artisdom/macro-keyboard/firmware/main/ble.c

/* This example code is in the Public Domain (or CC0 licensed, at your option.)
   Unless required by applicable law or agreed to in writing, this software is
   distributed on an "AS IS" BASIS, WITHOUT WARRANTIES OR
   CONDITIONS OF ANY KIND, either express or implied.
*/

#include <stdio.h>
#include <stdlib.h>
#include <string.h>
#include "freertos/FreeRTOS.h"
#include "freertos/task.h"
#include "freertos/event_groups.h"
#include "esp_system.h"
#include "esp_wifi.h"
#include "esp_event.h"
#include "esp_log.h"
#include "esp_bt.h"
#include "esp_bt_defs.h"
#include "esp_gap_ble_api.h"
#include "esp_gatts_api.h"
#include "esp_gatt_defs.h"
#include "esp_bt_main.h"
#include "esp_bt_device.h"
#include "driver/gpio.h"
#include "nvs_flash.h"

#include "esp_hidd_prf_api.h"
#include "hid_dev.h"

#include "ble.h"
#include "config.h"
#include "memory.h"
#include "events.h"



/* --------- Global Variables --------- */
TaskHandle_t xBLE_keyboard_task;
TaskHandle_t xBLE_media_task;
TaskHandle_t xBLE_battery_task;
TaskHandle_t xBLE_event_task;

// Input queue for sending keyboard reports
QueueHandle_t ble_keyboard_q;
// Input queue for sending media/Consumer control reports
QueueHandle_t ble_media_q;
// Input queue for sending battery reports
QueueHandle_t ble_battery_q;
// Input queue for receiving ble events to handle
QueueHandle_t ble_event_q;


/* --------- Local Defines --------- */
#define CHAR_DECLARATION_SIZE   (sizeof(uint8_t))  


/* --------- Local Variables --------- */
static const char *TAG = "ble";

static bool initialized = false;
static uint16_t hid_conn_id = 0;
static bool sec_conn = false;

static uint8_t current_host_id = 0;
static bt_host_t current_host;

static uint8_t hidd_service_uuid128[] = {
    /* LSB <--------------------------------------------------------------------------------> MSB */
    //first uuid, 16bit, [12],[13] is the value
    0xfb, 0x34, 0x9b, 0x5f, 0x80, 0x00, 0x00, 0x80, 0x00, 0x10, 0x00, 0x00, 0x12, 0x18, 0x00, 0x00,
};

static esp_ble_adv_data_t hidd_adv_data = {
    .set_scan_rsp = false,
    .include_name = true,
    .include_txpower = true,
    .min_interval = 0x0006, //slave connection min interval, Time = min_interval * 1.25 msec
    .max_interval = 0x0010, //slave connection max interval, Time = max_interval * 1.25 msec
    .appearance = 0x03c0,       //HID Generic,
    .manufacturer_len = 0,
    .p_manufacturer_data =  NULL,
    .service_data_len = 0,
    .p_service_data = NULL,
    .service_uuid_len = sizeof(hidd_service_uuid128),
    .p_service_uuid = hidd_service_uuid128,
    .flag = 0x6,
};

static esp_ble_adv_params_t hidd_adv_params = {
    .adv_int_min        = 0x20,
    .adv_int_max        = 0x30,
    .adv_type           = ADV_TYPE_IND,
    .own_addr_type      = BLE_ADDR_TYPE_PUBLIC,
    // .peer_addr          = {0x00, 0x00, 0x00, 0x00, 0x00, 0x00},
    // .peer_addr_type     = BLE_ADDR_TYPE_PUBLIC,
    .channel_map        = ADV_CHNL_ALL,
    .adv_filter_policy  = ADV_FILTER_ALLOW_SCAN_ANY_CON_ANY,
};



/* --------- Local Function --------- */
static void ble__hidd_event_callback(esp_hidd_cb_event_t event, esp_hidd_cb_param_t *param);
static void ble__gap_event_handler(esp_gap_ble_cb_event_t event, esp_ble_gap_cb_param_t *param);
static esp_err_t ble__start_advertising(esp_ble_adv_params_t *adv_params);

static void ble__set_host(uint8_t host_id);
static void ble__set_host_adv_params(bt_host_t host);

static uint8_t ble__get_last_host();
static void ble__set_last_host(uint8_t host_id);

static void ble__change_host(uint8_t host_id);
static void ble__save_host(bt_host_t host);



static void ble__hidd_event_callback(esp_hidd_cb_event_t event, esp_hidd_cb_param_t *param) {
    switch(event) {
        case ESP_HIDD_EVENT_REG_FINISH: {
            if (param->init_finish.state == ESP_HIDD_INIT_OK) {
                // esp_bd_addr_t rand_addr = {0x04,0x11,0x11,0x11,0x11,0x05};
                // esp_ble_gap_set_rand_addr(rand_addr);
                // esp_ble_gap_clear_whitelist();
                esp_ble_gap_set_device_name(BLE_DEVICE_NAME);
                esp_ble_gap_config_adv_data(&hidd_adv_data);

            }
            break;
        }
        case ESP_BAT_EVENT_REG: {
            break;
        }
        case ESP_HIDD_EVENT_DEINIT_FINISH:
            break;
        case ESP_HIDD_EVENT_BLE_CONNECT: {
            ESP_LOGI(TAG, "ESP_HIDD_EVENT_BLE_CONNECT");
            hid_conn_id = param->connect.conn_id;
            break;
        }
        case ESP_HIDD_EVENT_BLE_DISCONNECT: {
            sec_conn = false;
            ESP_LOGI(TAG, "ESP_HIDD_EVENT_BLE_DISCONNECT");
            ble__start_advertising(&hidd_adv_params);
            break;
        }
        case ESP_HIDD_EVENT_BLE_VENDOR_REPORT_WRITE_EVT: {
            ESP_LOGI(TAG, "%s, ESP_HIDD_EVENT_BLE_VENDOR_REPORT_WRITE_EVT", __func__);
            ESP_LOG_BUFFER_HEX(TAG, param->vendor_write.data, param->vendor_write.length);
        }
        default:
            break;
    }
    return;
}


static void ble__gap_event_handler(esp_gap_ble_cb_event_t event, esp_ble_gap_cb_param_t *param){
    switch (event) {
    case ESP_GAP_BLE_ADV_DATA_SET_COMPLETE_EVT:
        ble__start_advertising(&hidd_adv_params);
        break;
     case ESP_GAP_BLE_SEC_REQ_EVT:
        for(int i = 0; i < ESP_BD_ADDR_LEN; i++) {
             ESP_LOGD(TAG, "%x:",param->ble_security.ble_req.bd_addr[i]);
        }
        esp_ble_gap_security_rsp(param->ble_security.ble_req.bd_addr, true);
     break;
     case ESP_GAP_BLE_AUTH_CMPL_EVT:
        sec_conn = true;
        bt_host_t host;

        memcpy(host.addr, param->ble_security.auth_cmpl.bd_addr, sizeof(esp_bd_addr_t));
        host.type = param->ble_security.auth_cmpl.addr_type;

        ESP_LOGI(TAG, "remote host address: "ESP_BD_ADDR_STR, ESP_BD_ADDR_HEX(host.addr));
        ESP_LOGI(TAG, "address type = %d", host.type);
        ESP_LOGI(TAG, "pair status = %s",param->ble_security.auth_cmpl.success ? "success" : "fail");
        if(!param->ble_security.auth_cmpl.success) {
            ESP_LOGE(TAG, "fail reason = 0x%x",param->ble_security.auth_cmpl.fail_reason);
            sec_conn = false;
            break;
        }

        // only save if address is Public or Random
        if (host.type <= BLE_ADDR_TYPE_RANDOM) {
            ble__save_host(host);
        }
        else {
            ESP_LOGW(TAG, "Unable to save host in memory as the addr type is %d", host.type);
        }

        event_t event = {
            .type = EVENT_BT_CONNECTED,
            .data = current_host_id,
        };
        xQueueSend(event_q, (void *) &event, (TickType_t) 0);

        break;
    case ESP_GAP_BLE_REMOVE_BOND_DEV_COMPLETE_EVT:
        ESP_LOGI(TAG, "Removed bond device: %d "ESP_BD_ADDR_STR, param->remove_bond_dev_cmpl.status, ESP_BD_ADDR_HEX(param->remove_bond_dev_cmpl.bd_addr));
        break;
    default:
        // ESP_LOGD(TAG, "gap event handler: %d", *((int *)&event));
        break;
    }
}


// wrapper to call ble internal api and send an event to main event handler
static esp_err_t ble__start_advertising(esp_ble_adv_params_t *adv_params) {

    event_t event;

    if (adv_params->peer_addr[0] == 0) { // terrible check
        event.type = EVENT_BT_ADV_ALL;
    }
    else {
        event.type = EVENT_BT_ADV;
    }
    // event.type = EVENT_LEDS_BT_ADV;
    event.data = current_host_id;
    xQueueSend(event_q, (void *) &event, (TickType_t) 0);

    return esp_ble_gap_start_advertising(adv_params);
}


static uint8_t ble__get_last_host() {
    return memory__get_bluetooth_last_host();
}

static void ble__set_last_host(uint8_t host_id) {
    memory__set_bluetooth_last_host(host_id);
}


static void ble__set_host_adv_params(bt_host_t host) {

    memcpy(hidd_adv_params.peer_addr, host.addr, sizeof(host.addr));
    hidd_adv_params.peer_addr_type = host.type;
    hidd_adv_params.adv_type = ADV_TYPE_DIRECT_IND_LOW;

    ESP_LOGD(TAG, "adv peer addr: "ESP_BD_ADDR_STR, ESP_BD_ADDR_HEX(hidd_adv_params.peer_addr));
    ESP_LOGD(TAG, "adv peer addr type: %d", hidd_adv_params.peer_addr_type);

    if (host.addr[0] == 0) { //terrible check
        ESP_LOGW(TAG, "No host stored in memory, advertising to all...");
        hidd_adv_params.adv_type = ADV_TYPE_IND;
    }

}


static void ble__set_host(uint8_t host_id) {

    bt_host_t host;

    ESP_LOGI(TAG, "Setting host to %d", host_id);

    host = memory__get_bluetooth_host(host_id);
    current_host = host;
    current_host_id = host_id;

    ble__set_host_adv_params(host);

}


static void ble__change_host(uint8_t host_id) {
    esp_err_t ret;
    bt_host_t previous_host = current_host;

    ESP_LOGI(TAG, "Changing host to %d", host_id);

    ESP_LOGD(TAG, "current host: "ESP_BD_ADDR_STR, ESP_BD_ADDR_HEX(current_host.addr));

    ret = esp_ble_gap_stop_advertising();
    if (ret) {
        ESP_LOGE(TAG, "gap stop advertising failed");
        return;
    }

    ble__set_host(host_id);
    
    ret = esp_ble_gap_disconnect(previous_host.addr);
    if (ret) {
        ESP_LOGE(TAG, "gap disconnect failed");
        return;
    }

    ret = ble__start_advertising(&hidd_adv_params);
    if (ret) {
        ESP_LOGE(TAG, "gap start advertising failed");
        return;
    }
}


static void ble__save_host(bt_host_t host) {
    ESP_LOGI(TAG, "Saving host at id %d", current_host_id);

    if (memcmp(&current_host, &host, sizeof(bt_host_t)) != 0) {
        ESP_LOGD(TAG, "Host is different, saving....");
        memory__set_bluetooth_host(current_host_id, host);
        ble__set_host_adv_params(host);
    }
    else {
        ESP_LOGD(TAG, "Host is the same, not saving");
    }
    ble__set_last_host(current_host_id);
}



void ble__init(void) {
    esp_err_t ret;

    ESP_LOGI(TAG, "Init BLE");

    // Create queues
    ble_keyboard_q = xQueueCreate(32, HID_REPORT_LEN * sizeof(uint8_t));
    ble_media_q = xQueueCreate(32, HID_CC_REPORT_LEN * sizeof(uint8_t));
    ble_battery_q = xQueueCreate(32, sizeof(uint8_t));
    ble_event_q = xQueueCreate(32, sizeof(bt_event_t));

    // set host to connect to
    current_host_id = ble__get_last_host();
    ble__set_host(current_host_id);

    // ESP_ERROR_CHECK(esp_bt_controller_mem_release(ESP_BT_MODE_CLASSIC_BT));

    if (initialized == false) {
        esp_bt_controller_config_t bt_cfg = BT_CONTROLLER_INIT_CONFIG_DEFAULT();
        ret = esp_bt_controller_init(&bt_cfg);
        if (ret) {
            ESP_LOGE(TAG, "%s initialize controller failed\n", __func__);
            return;
        }
    }

    ret = esp_bt_controller_enable(ESP_BT_MODE_BLE);
    if (ret) {
        ESP_LOGE(TAG, "%s enable controller failed\n", __func__);
        return;
    }

    if (initialized == false) {
        ret = esp_bluedroid_init();
        if (ret) {
            ESP_LOGE(TAG, "%s init bluedroid failed\n", __func__);
            return;
        }
        initialized = true;
    }

    ret = esp_bluedroid_enable();
    if (ret) {
        ESP_LOGE(TAG, "%s enable bluedroid failed\n", __func__);
        return;
    }

    if((ret = esp_hidd_profile_init()) != ESP_OK) {
        ESP_LOGE(TAG, "%s init hidd profile failed\n", __func__);
    }

    // register the callback function to the gap module
    esp_ble_gap_register_callback(ble__gap_event_handler);
    esp_hidd_register_callbacks(ble__hidd_event_callback);

    /* set the security iocap & auth_req & key size & init key response key parameters to the stack*/
    esp_ble_auth_req_t auth_req = ESP_LE_AUTH_BOND;     //bonding with peer device after authentication
    esp_ble_io_cap_t iocap = ESP_IO_CAP_NONE;           //set the IO capability to No output No input
    uint8_t key_size = 16;      //the key size should be 7~16 bytes
    uint8_t init_key = ESP_BLE_ENC_KEY_MASK | ESP_BLE_ID_KEY_MASK;
    uint8_t rsp_key = ESP_BLE_ENC_KEY_MASK | ESP_BLE_ID_KEY_MASK;
    esp_ble_gap_set_security_param(ESP_BLE_SM_AUTHEN_REQ_MODE, &auth_req, sizeof(uint8_t));
    esp_ble_gap_set_security_param(ESP_BLE_SM_IOCAP_MODE, &iocap, sizeof(uint8_t));
    esp_ble_gap_set_security_param(ESP_BLE_SM_MAX_KEY_SIZE, &key_size, sizeof(uint8_t));
    /* If your BLE device act as a Slave, the init_key means you hope which types of key of the master should distribute to you,
    and the response key means which key you can distribute to the Master;
    If your BLE device act as a master, the response key means you hope which types of key of the slave should distribute to you,
    and the init key means which key you can distribute to the slave. */
    esp_ble_gap_set_security_param(ESP_BLE_SM_SET_INIT_KEY, &init_key, sizeof(uint8_t));
    esp_ble_gap_set_security_param(ESP_BLE_SM_SET_RSP_KEY, &rsp_key, sizeof(uint8_t));

    // Create tasks
    xTaskCreatePinnedToCore(ble__keyboard_task, "ble_keyboard_task", BLE_KEYBOARD_TASK_STACK, NULL, BLE_KEYBOARD_TASK_PRIORITY, &xBLE_keyboard_task, 0);
    xTaskCreatePinnedToCore(ble__media_task, "ble_media_task", BLE_MEDIA_TASK_STACK, NULL, BLE_MEDIA_TASK_PRIORITY, &xBLE_media_task, 0);
    xTaskCreatePinnedToCore(ble__battery_task, "ble_battery_task", BLE_BATTERY_TASK_STACK, NULL, BLE_BATTERY_TASK_PRIORITY, &xBLE_battery_task, 0);
    xTaskCreatePinnedToCore(ble__event_task, "ble_event_task", BLE_EVENT_TASK_STACK, NULL, BLE_EVENT_TASK_PRIORITY, &xBLE_event_task, 0);
}


esp_err_t ble__deinit() {
    esp_err_t ret;

    ESP_LOGI(TAG, "Deinit BLE");

    ESP_LOGI(TAG, "Deleting BLE tasks");
    if (xBLE_keyboard_task != NULL) {
        ESP_LOGW(TAG, "Stopping keyboard task");
        vTaskDelete(xBLE_keyboard_task);
        xBLE_keyboard_task = NULL;
    }
    if (xBLE_media_task != NULL) {
        ESP_LOGW(TAG, "Stopping media task");
        vTaskDelete(xBLE_media_task);
        xBLE_media_task = NULL;
    }
    if (xBLE_battery_task != NULL) {
        ESP_LOGW(TAG, "Stopping battery task");
        vTaskDelete(xBLE_battery_task);
        xBLE_battery_task = NULL;
    }
    if (xBLE_event_task != NULL) {
        ESP_LOGW(TAG, "Stopping event task");
        vTaskDelete(xBLE_event_task);
        xBLE_event_task = NULL;
    }

    ret = esp_hidd_profile_deinit();
    if (ret) {
        ESP_LOGE(TAG, "deinit hidd profile failed");
        return ret;
    }

    ret = esp_bluedroid_disable();
    if (ret) {
        ESP_LOGE(TAG, "disable bluedroid failed");
        return ret;
    }

    ret = esp_bt_controller_disable();
    if (ret) {
        ESP_LOGE(TAG, "disable controller failed");
        return ret;
    }

    ESP_LOGI(TAG, "Deleting BLE queues");
    vQueueDelete(ble_keyboard_q);
    vQueueDelete(ble_media_q);
    vQueueDelete(ble_battery_q);
    vQueueDelete(ble_event_q);

    ESP_LOGI(TAG, "Successful BLE deinit");

    return ESP_OK;
}








void ble__keyboard_task(void *pvParameters) {

    uint8_t report[HID_REPORT_LEN];

    ESP_LOGI(TAG, "Starting ble keyboard task");

    if (ble_keyboard_q == NULL) {
        ESP_LOGW(TAG, "keyboard queue not initialised, resetting...");
        xQueueReset(ble_keyboard_q);
    }

    while (1) {
        //check if queue is initialized
        if (ble_keyboard_q != NULL) {
            //pend on MQ, if timeout triggers, just wait again.
            if (xQueueReceive(ble_keyboard_q, &report, (TickType_t) 100)) {
                //if we are not connected, discard.
                if (sec_conn == false)
                    continue;
                // esp_hidd_send_keyboard_value(hid_conn_id, 0, &report, HID_REPORT_LEN);
                hid_dev_send_report(hidd_le_env.gatt_if, hid_conn_id, HID_RPT_ID_KEY_IN, HID_REPORT_TYPE_INPUT, HID_REPORT_LEN, report);
            }
        }
        else {
            ESP_LOGE(TAG, "keyboard queue not initialized, retry in 1s");
            vTaskDelay(1000 / portTICK_PERIOD_MS);
        }
    }

    ESP_LOGW(TAG, "Stopping ble keyboard task");
    vTaskDelete(NULL);

}


void ble__media_task(void *pvParameters) {

    uint8_t report[HID_CC_REPORT_LEN];

    ESP_LOGI(TAG, "Starting ble media task");

    if (ble_media_q == NULL) {
        ESP_LOGW(TAG, "media queue not initialised, resetting...");
        xQueueReset(ble_media_q);
    }

    while (1) {
        //check if queue is initialized
        if (ble_media_q != NULL) {
            //pend on MQ, if timeout triggers, just wait again.
            if (xQueueReceive(ble_media_q, &report, (TickType_t) 100)) {
                //if we are not connected, discard.
                if (sec_conn == false)
                    continue;
                ESP_LOGD(TAG, "media report: 0x%x 0x%x", report[0], report[1]);
                esp_hidd_send_consumer_value(hid_conn_id, report[0], report[1]);
            }
        }
        else {
            ESP_LOGE(TAG, "media queue not initialized, retry in 1s");
            vTaskDelay(1000 / portTICK_PERIOD_MS);
        }
    }

    ESP_LOGW(TAG, "Stopping ble media task");
    vTaskDelete(NULL);

}


void ble__battery_task(void *pvParameters) {

    uint8_t battery_report;

    ESP_LOGI(TAG, "Starting ble battery task");

    if (ble_battery_q == NULL) {
        ESP_LOGW(TAG, "battery queue not initialised, resetting...");
        xQueueReset(ble_battery_q);
    }

    while(1) {
        //check if queue is initialized
        if (ble_media_q != NULL) {
            //pend on MQ, if timeout triggers, just wait again.
            if (xQueueReceive(ble_battery_q, &battery_report, (TickType_t) 100)) {
                ESP_LOGD(TAG, "battery report: %d%%", battery_report);
                esp_ble_gatts_set_attr_value(42, sizeof(uint8_t), &battery_report);
                //Only send if we are connected
                if (sec_conn) {
                    ESP_LOGD(TAG, "Sending battey report");
                    esp_ble_gatts_send_indicate(hidd_le_env.gatt_if, hid_conn_id, 42, sizeof(uint8_t), &battery_report, false);
                }
            }
        }
        else {
            ESP_LOGE(TAG, "battery queue not initialized, retry in 1s");
            vTaskDelay(1000 / portTICK_PERIOD_MS);
        }
    }

    ESP_LOGW(TAG, "Stopping ble battery task");
    vTaskDelete(NULL);

}


void ble__event_task(void *pvParameters) {

    // only BT host id change for now
    bt_event_t event;
    bt_host_t host;

    ESP_LOGI(TAG, "Starting ble event task");

    if (ble_event_q == NULL) {
        ESP_LOGW(TAG, "ble_event queue not initialised, resetting...");
        xQueueReset(ble_event_q);
    }

    while (1) {
        //check if queue is initialized
        if (ble_event_q != NULL) {
            //pend on MQ, if timeout triggers, just wait again.
            if (xQueueReceive(ble_event_q, &event, (TickType_t) 100 )) {

                switch (event.type) {
                    case BT_EVENT_CHANGE_HOST: {
                        ESP_LOGD(TAG, "Event: Change host");
                        ble__change_host(event.host_id);
                        break;
                    }
                    case BT_EVENT_RESET_HOST: {
                        ESP_LOGD(TAG, "Event: Reset host");
                        // host = memory__get_bluetooth_host(event.host_id);
                        // ESP_LOGD(TAG, "Removing bond device with addr: "ESP_BD_ADDR_STR, ESP_BD_ADDR_HEX(host.addr));
                        // esp_ble_remove_bond_device(host.addr);

                        memset(&host, 0x00, sizeof(bt_host_t));
                        memory__set_bluetooth_host(event.host_id, host);
                        ble__change_host(event.host_id);
                        break;
                    }
                    default: {
                        ESP_LOGW(TAG, "Unhandled event type");
                        break;
                    }
                }
            }
        }
        else {
            ESP_LOGE(TAG, "ble_event queue not initialized, retry in 1s");
            vTaskDelay(1000 / portTICK_PERIOD_MS);
        }
    }

    ESP_LOGW(TAG, "Stopping ble event task");
    vTaskDelete(NULL);

}
